edgecollective/four-probe/v_0.9/v_0.9_mockup.png

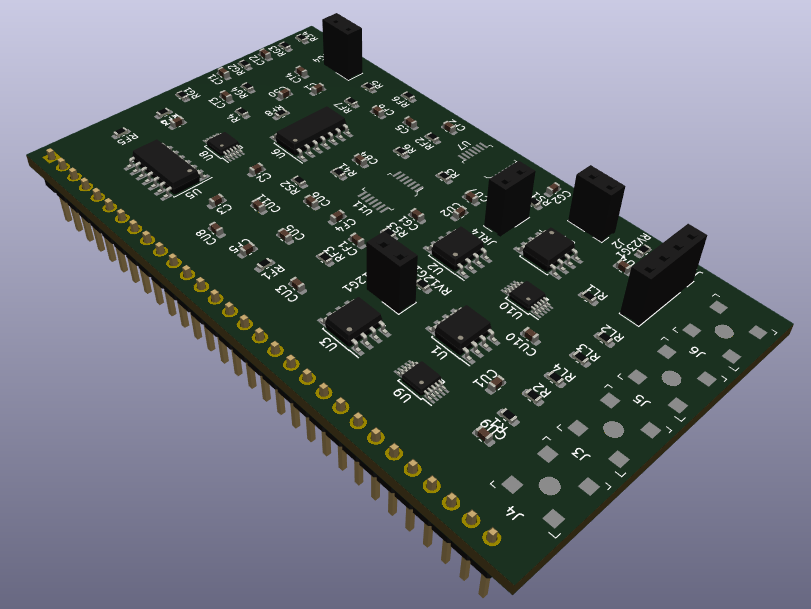
v_0.9/v_0.9_mockup.png
