edgecollective/four-probe/v_0.9/python_capture/exp1/plot.pdf

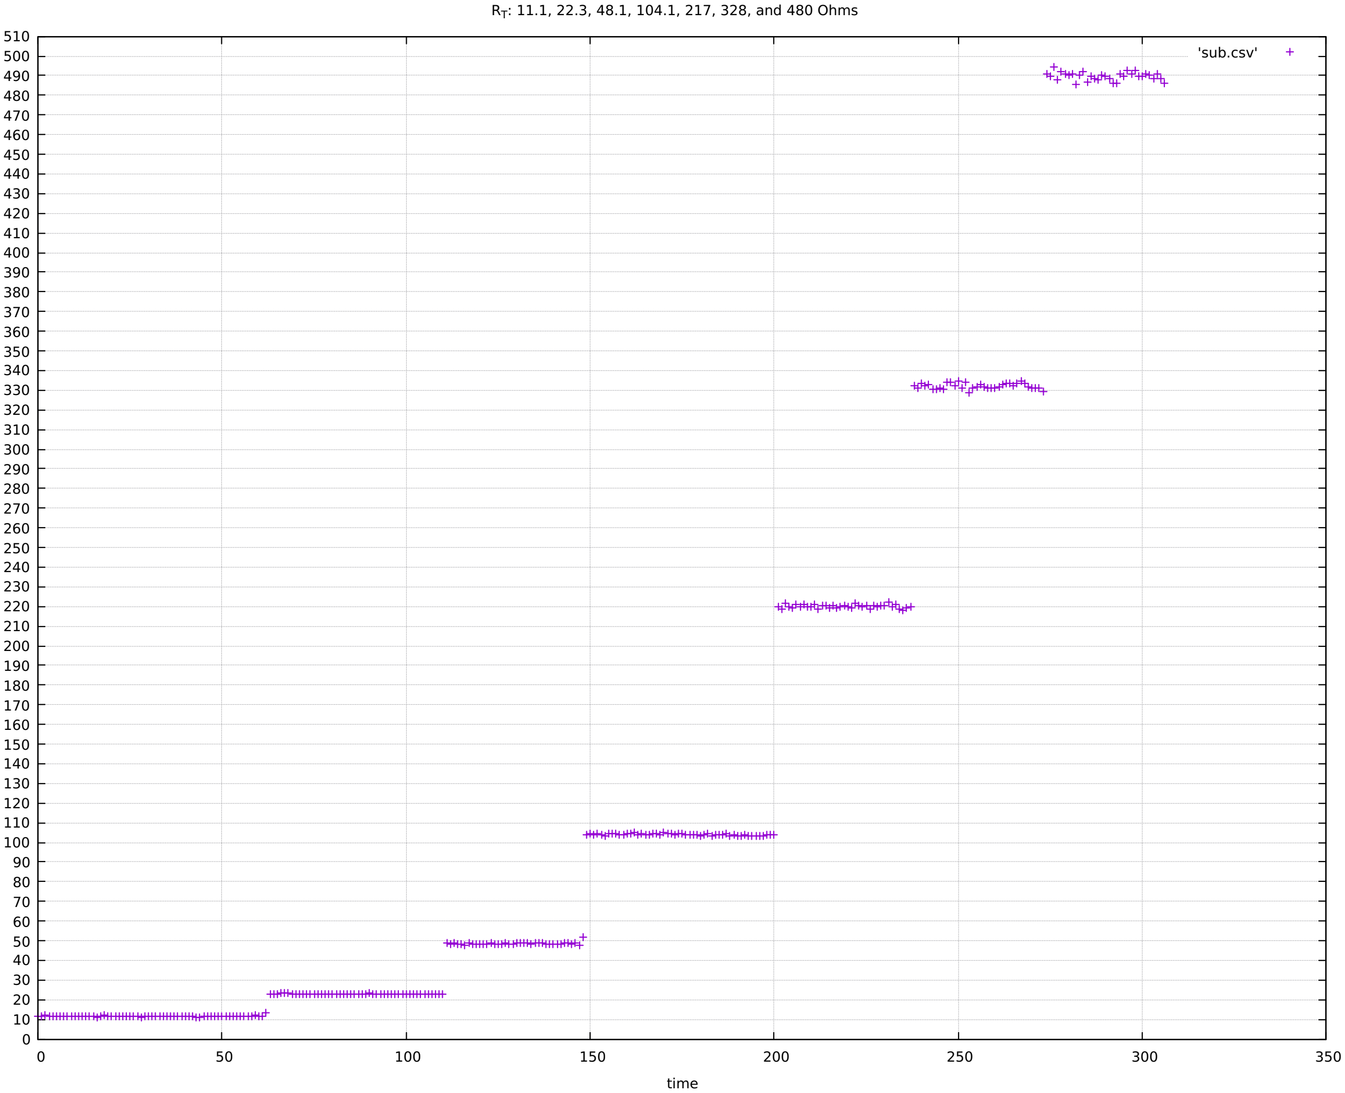
[picture p3: figure]
tim

resistance
