edgecollective/four-probe/v_0.9/adg1211.png

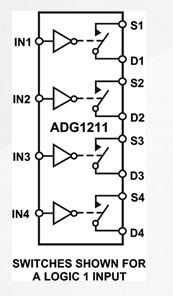
v_0.9/adg1211.png
