edgecollective/four-probe/v_0.9/artwork.png

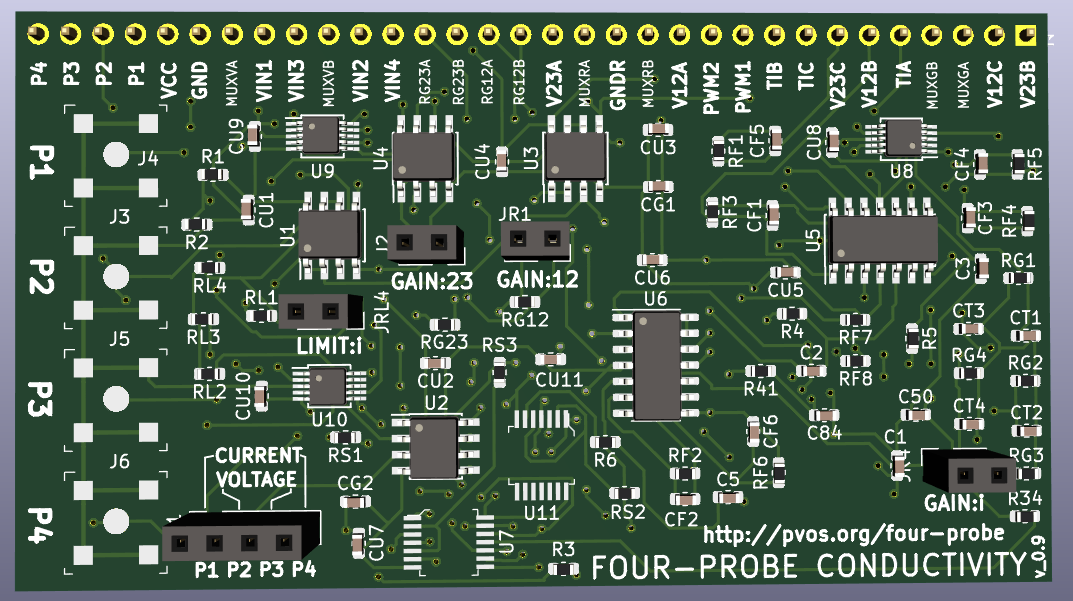
v_0.9/artwork.png
