edgecollective/four-probe/v_0.9/chat.png

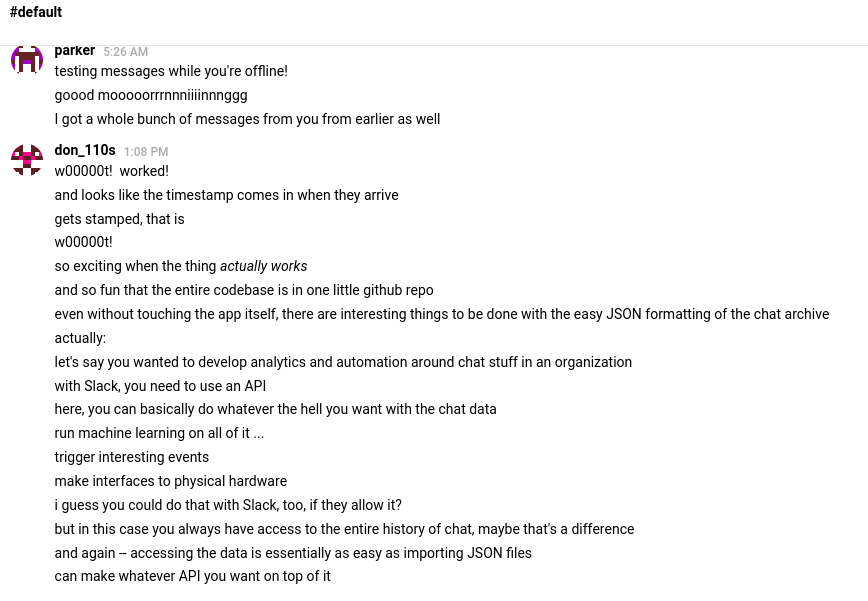
v_0.9/chat.png
