edgecollective/four-probe/v_0.9/feather_adapter/board_layout.png

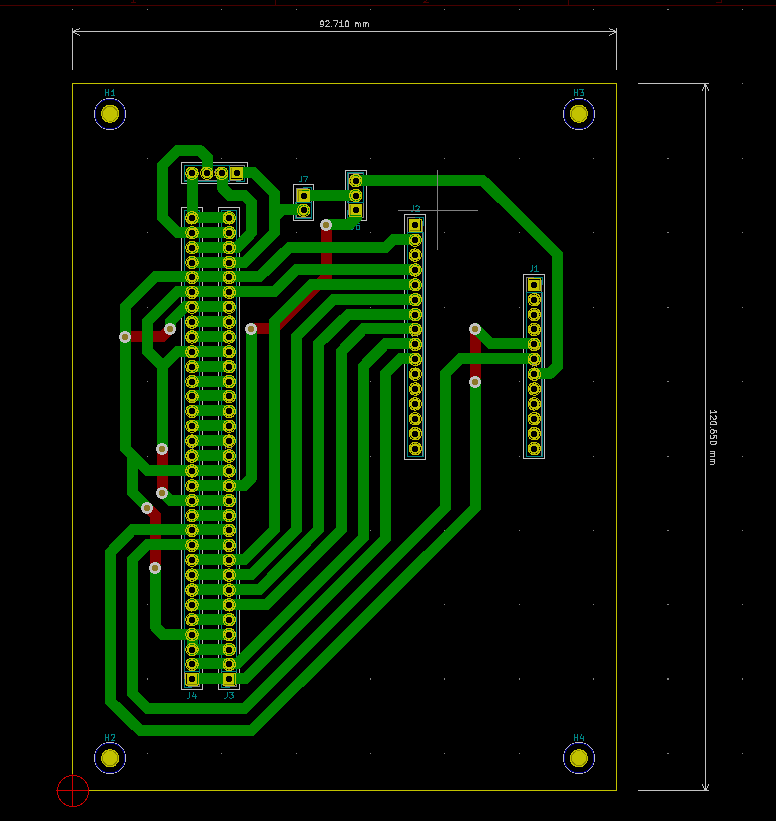
v_0.9/feather_adapter/board_layout.png
