edgecollective/four-probe/v_0.9/firmware/conversions/sineout.png

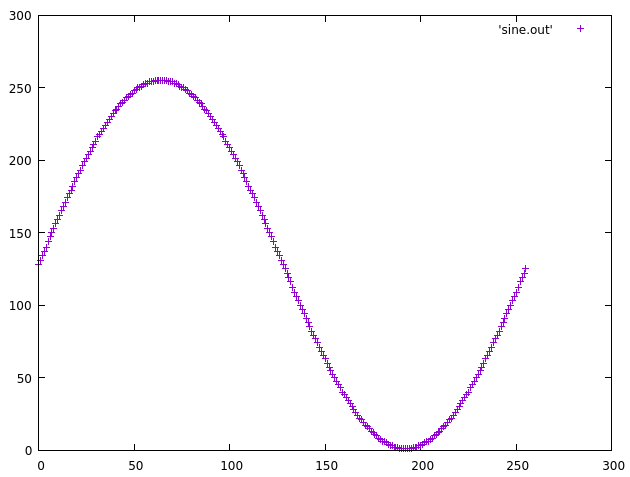
v_0.9/firmware/conversions/sineout.png
