edgecollective/four-probe/v_0.9/four_probe_0.9_mockup_top.png

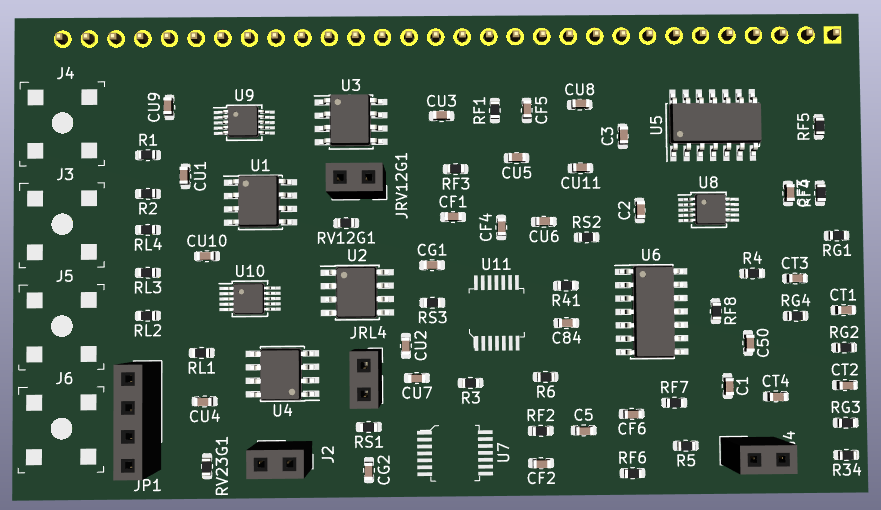
v_0.9/four_probe_0.9_mockup_top.png
