edgecollective/four-probe/v_0.9/track_hold.png

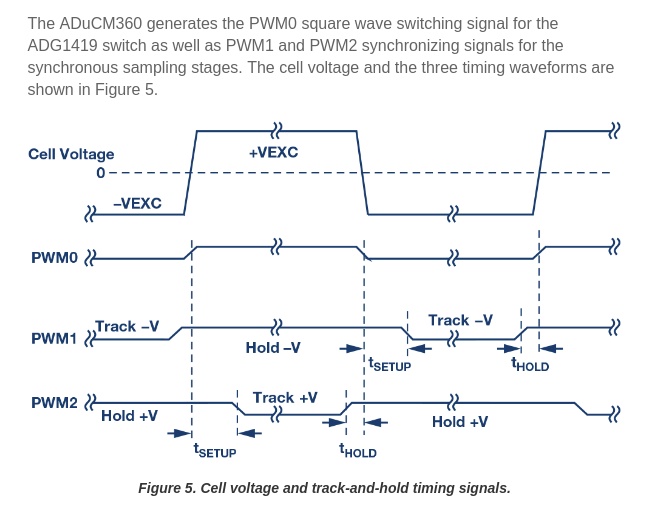
v_0.9/track_hold.png
