edgecollective/four-probe/v_0.9/4probe_v_0.5.pdf/four_probe.pdf

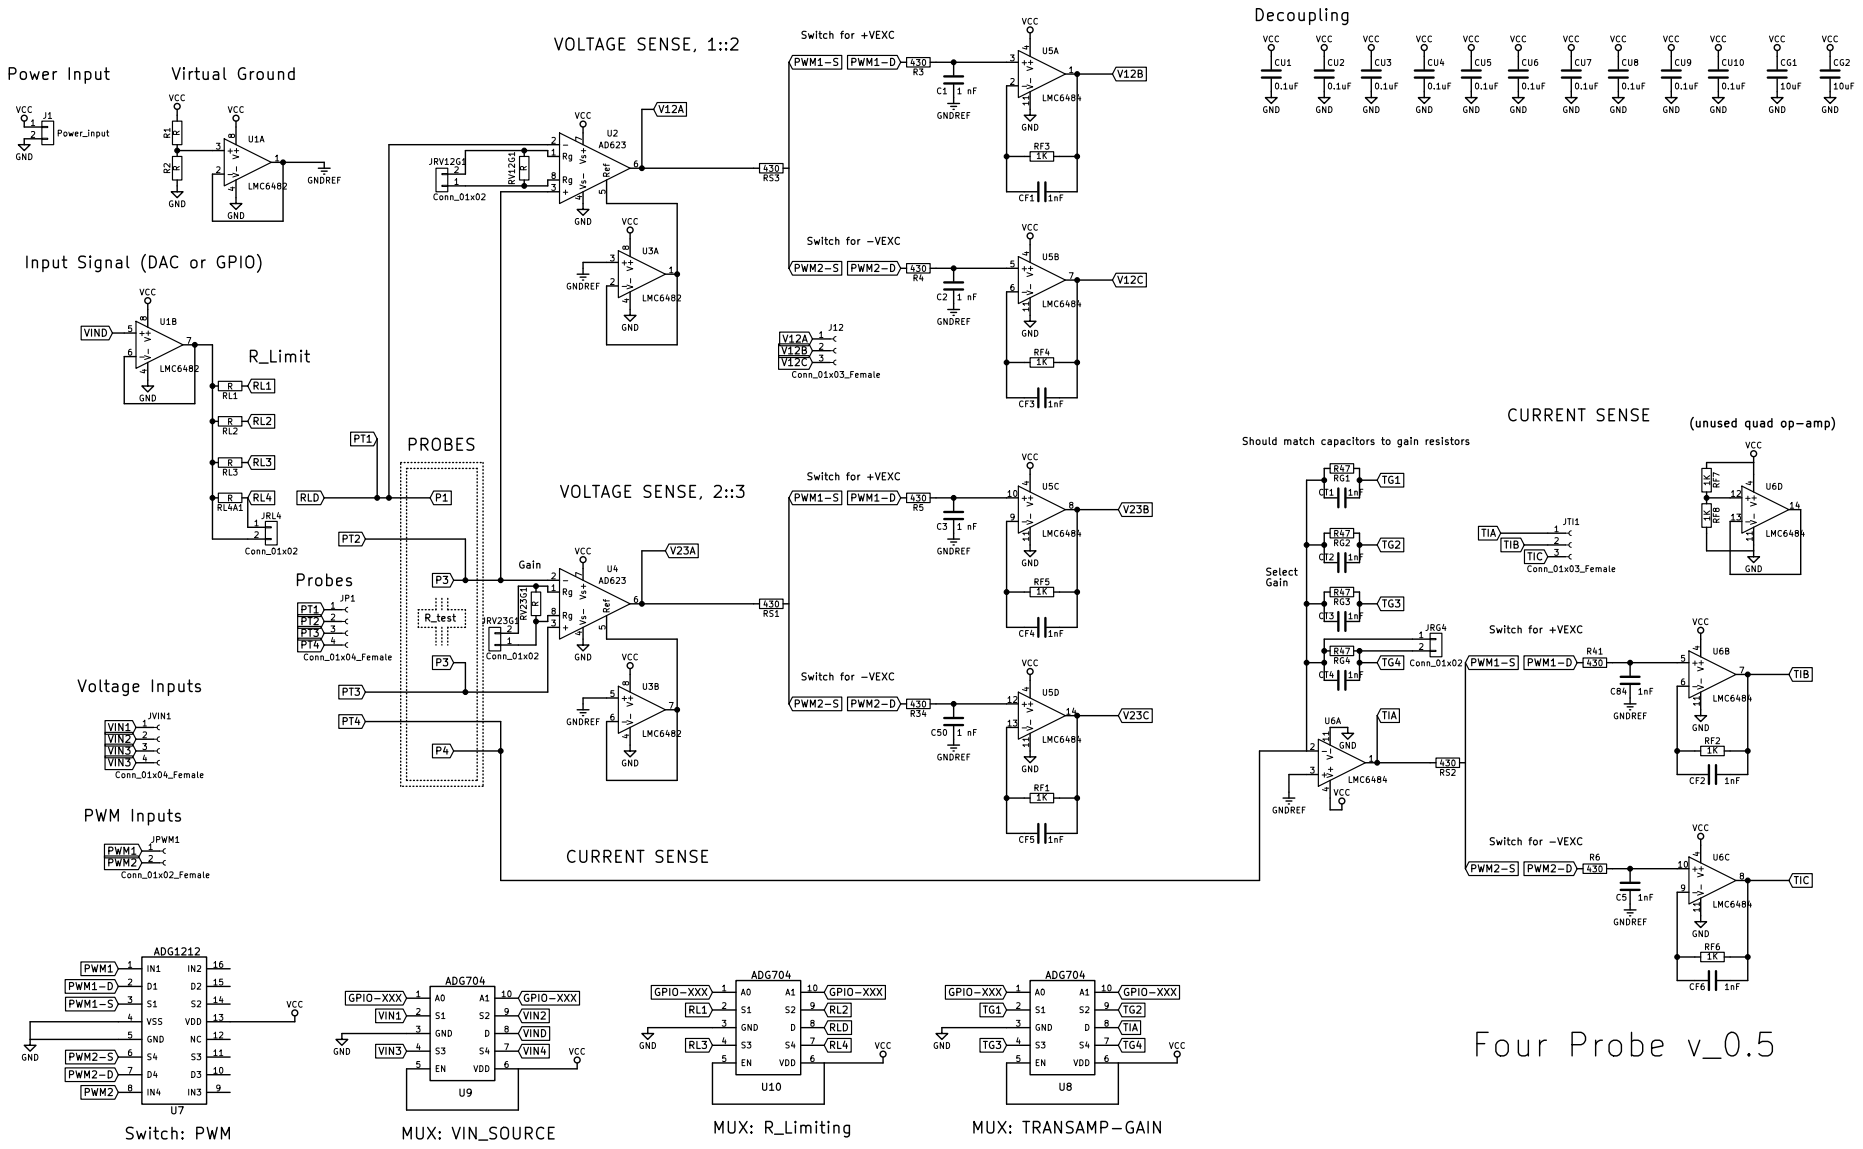
[picture p20: page 1]
