edgecollective/four-probe/v_0.9/four_probe_v_0.4.pdf

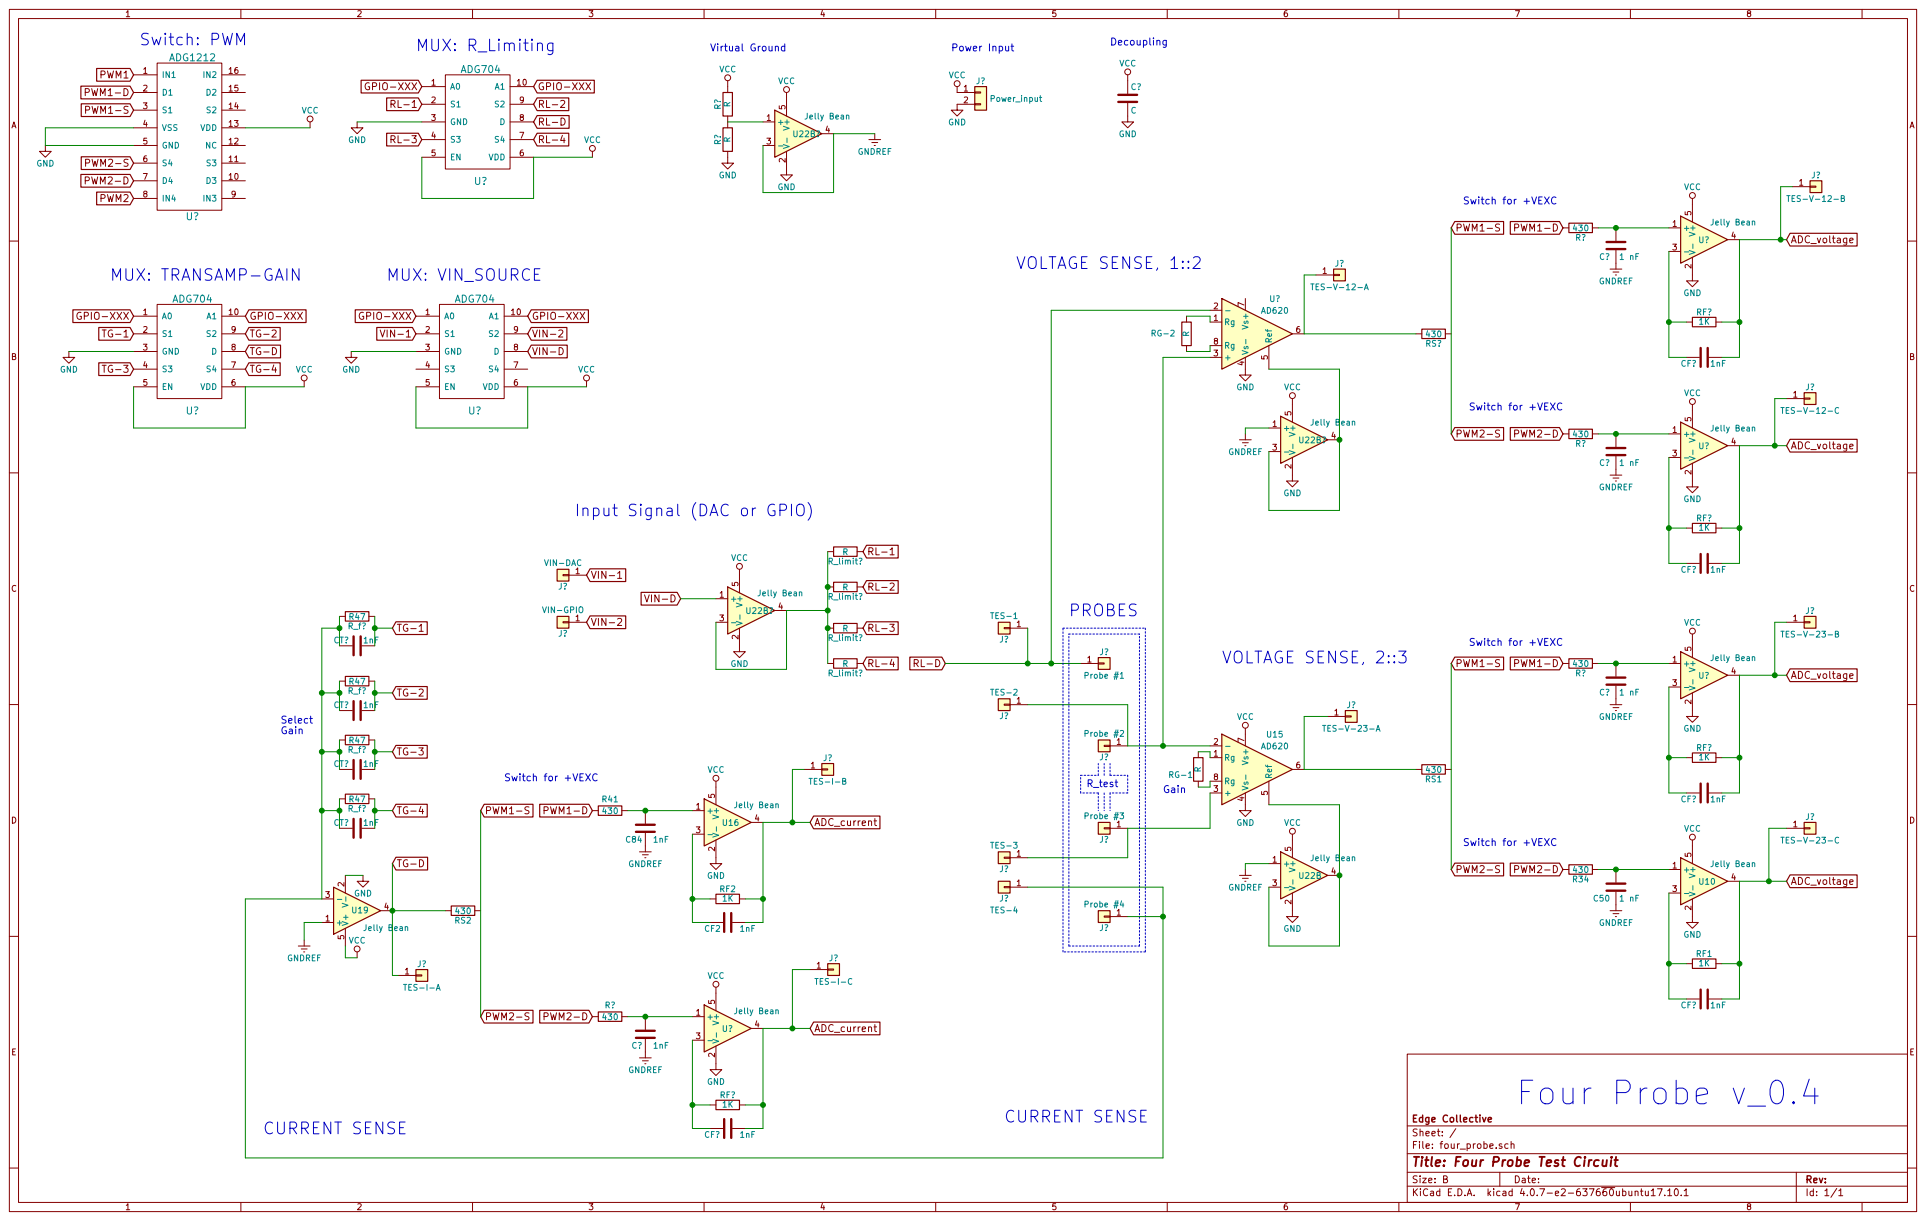
[picture p21: page 1]
